sa9ra1xken/KeyboardHook/Arduino/KeyboardHook/AsciiCode.h

#define ASC_NUL 0x00
#define ASC_SOH 0x01 //^A
#define ASC_STX 0x02 //^B
#define ASC_ETX 0x03 //^C
#define ASC_EOT 0x04 //^D
#define ASC_ENQ 0x05 //^E
#define ASC_ACK 0x06
#define ASC_BS  0x08
#define ASC_HT  0x09
#define ASC_LF  0x0A
#define ASC_CR  0x0D
#define ASC_ESC 0x1B //^F
#define ASC_SPC 0x20
#define ASC_DEL 0x7F
