sa9ra1xken/KeyboardHook/Arduino/KeyboardHook/ScanCode.h

#define SFT_UP 0x40
#define SFT_CODE 0x80

#define KEY_NOP 0x00
#define KEY_SHIFT 0x01
#define KEY_LOCK 0x02

#define ALPH_A 0x08
#define ALPH_B 0x09
#define ALPH_C 0x0a
#define ALPH_D 0x0b
#define ALPH_E 0x0c
#define ALPH_F 0x0d
#define ALPH_G 0x0e
#define ALPH_H 0x0f

#define ALPH_I 0x10
#define ALPH_J 0x11
#define ALPH_K 0x12
#define ALPH_L 0x13
#define ALPH_M 0x14
#define ALPH_N 0x15
#define ALPH_O 0x16
#define ALPH_P 0x17

#define ALPH_Q 0x18
#define ALPH_R 0x19
#define ALPH_S 0x1a
#define ALPH_T 0x1b
#define ALPH_U 0x1c
#define ALPH_V 0x1d
#define ALPH_W 0x1e
#define ALPH_X 0x1f

#define ALPH_Y 0x20
#define ALPH_Z 0x21
#define NUM_0 0x22
#define NUM_1 0x23
#define NUM_2 0x24
#define NUM_3 0x25
#define NUM_4 0x26
#define NUM_5 0x27

#define NUM_6 0x28
#define NUM_7 0x29
#define NUM_8 0x2a
#define NUM_9 0x2b
#define KEY_COMMA 0x2c
#define KEY_QUOTE 0x2d
#define KEY_SEMICOL 0x2e
#define KEY_PERIOD 0x2f

#define KEY_SLASH 0x30
#define KEY_CIRCUMFLEX 0x31
#define KEY_MINUS 0x32
#define KEY_EQUAL 0x33
#define KEY_CENT 0x34
#define KEY_GRAVE 0x35
#define KEY_DEGREE 0x36
#define KEY_SPACE 0x37

#define KEY_TAB 0x38
#define KEY_DEL 0x39
#define KEY_RETURN 0x3A
#define KEY_REROC 0x3B
#define KEY_BS 0x3C
#define KEY_CODE 0x3D
